IQTLabs/AISonobuoy/docs/img/sixfab_buoy.jpg

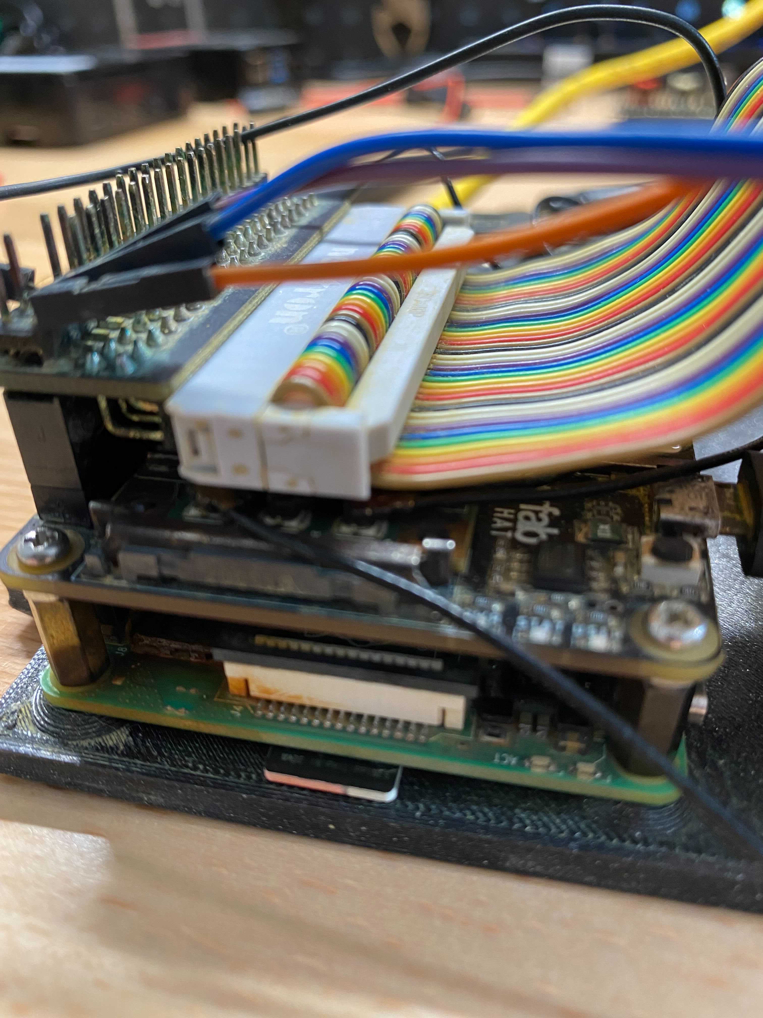
docs/img/sixfab_buoy.jpg
