IQTLabs/AISonobuoy/Hydrophone/Featherwing Interface/v1.2 - Fabbed/board-v1.2.png

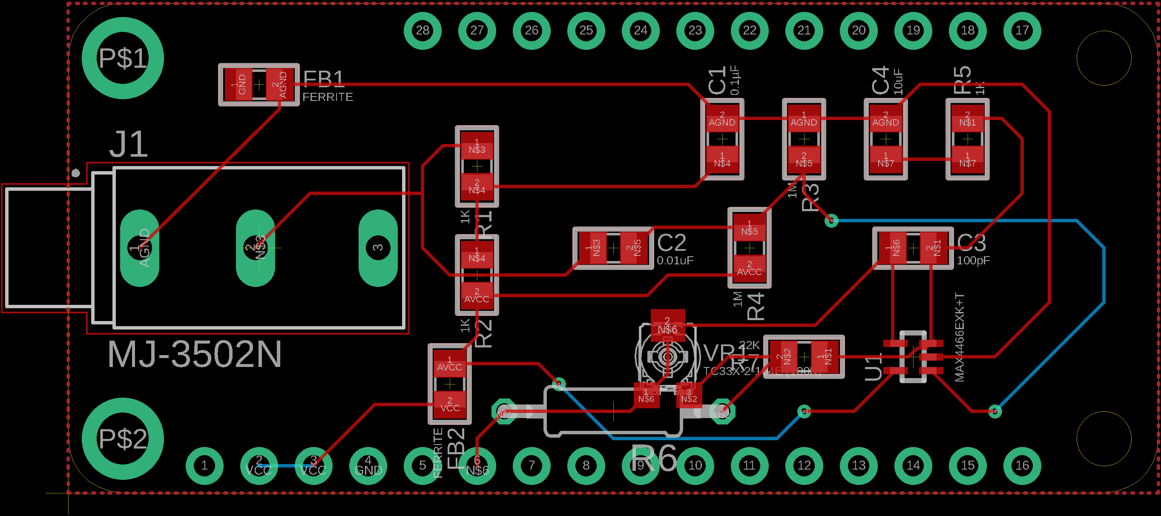
Hydrophone/Featherwing Interface/v1.2 - Fabbed/board-v1.2.png
